ozgurgulsuna/ELE713-SwitchedPowerSupplies/[03] Simulation/Close-Loop-Forward-Converter-CONTROL.asc

B1: bv; V=V(Vi)
B3: bv; V= if(V(Vin) >50,0, 5)
C1: cap; {Cf}; Rser=28m
C2: cap; 100µ
C3: cap; 2.2n
C4: cap; 2.2n
C5: cap; 0.1µ
C6: cap; 22µ
C7: cap; 10n
C8: cap; 10n
D1: diode
D2: diode; RFUH25NS3S
D156: diode; D1
ind1: ind2; {L1}; Rser=20m
ind2: ind2; {L2}; Rser=20m
ind3: ind2; {L3}; Rser=20m
L4: ind2; {Lf}; Rser=15m
M1: nmos; IPB200N25N3
R1: res; 100
R2: res; {10*RL}
R4: res; 47
R5: res; 4.7k
R6: res; 100k
R7: res; 160k
R8: res; 178k
R9: res; 12k
R10: res; 18k
R11: res; 240k
R12: res; 10k
R13: res; 25k
R14: res; 10k
R15: res; 8.2k
R16: res; 4.7k
R17: res; 20k
R20: res; 39
R21: res; 1Meg
R22: res; 10k
R24: res; 0.6944
R26: res; 0
R30: res; 10k
Rs: res; 8m
S1: sw; NMOS
U1: LT1952-1
U3: tl431
U5: PC817C
V1: voltage; 11
V2: voltage; 12
Vi: voltage; PWL(0 0 0.499m 0 0.5m 36 1m 36 2m 36 2.01m 60)
Named nets: Vaux, 0, FB, Vref, SEC, Vi, Vin, VccBias, Sout, FWD
.model NMOS SW(Ron=25m Roff=1Meg Vt=.5 Vh=-.4)
.model D1 D(Ron=20m Roff=100G Vfwd=0.1)
.tran 0 0.1 0 1e-7 startup
K1 ind1 ind2 ind3 1
.param L1 190u
.param L2  30.4u
.param L3 190u
.param L4 94u
.param fs  200k
.param Cf 220u
.param RL 0.625
.param Lf 20u
.param Laux 20u
.param Caux 20u
.ic V(C10) = 8
.ic V(Vaux) = 8
.ic V(C2) = 8
.model HAT2266 VDMOS(Rg=0.5 Vto=2.3 Rd=4m Rs=1m Rb=5m Kp=70 lambda=.05 Cgdmax=0.65n Cgdmin=.08n Cgs=3.455n Cjo=1.2n Is=120p ksubthres=.1 mfg=Furkan Vds=60 Ron=12m Qg=25n)
*****************************************************************************
* TL431 MACROMODEL ***************3-26-92************************************
* REV N/A ****************************************************************DBB
*****************************************************************************
*               REFERENCE
*               |  ANODE
*               |  |  CATHODE
*               |  |  |
*.SUBCKT  TL431 1  2  3
* Reverse symbol
* Anode Cathode Ref   adjusted to LTSPICE symbol
.SUBCKT  TL431 2 3 1
V1  6  7  DC  1.4V
I1  2  4  1E-3
R1  1  2  1.2E6
R2  4  2  RMOD 2.495E3
R3  5  7  .2
D1  3  6  DMOD1
D2  2  3  DMOD1
D3  2  7  DMOD2
E1  5  2  POLY(2)  (4,2)  (1,2)  0  710  -710
.MODEL RMOD RES (TC1=1.4E-5 TC2=-1E-6)
.MODEL DMOD1 D (RS=.3)
.MODEL DMOD2 D (RS=1E-6)
.ENDS
