ozgurgulsuna/ELE713-SwitchedPowerSupplies/[03] Simulation/Close-Loop-Forward-Converter-REALISTIC.asc

B1: bv; V=V(Vi)
B2: bv; V=if(V(Vc,SEC)<12, V(Vc,SEC), 12)
B3: bv; V= if(V(Vin) >50,0, 5)
C1: cap; {Cf}; Rser=28m
C2: cap; 100µ
C3: cap; 2.2n
C4: cap; 2.2n
C5: cap; 0.1µ
C6: cap; 22µ
C7: cap; 5n
C8: cap; 1n
C9: cap; 22µ; Rser=2m
C10: cap; 1µ
C12: cap; 10µ
C13: cap; 220pF
C14: cap; 10µ
C15: cap; 100p
C16: cap; 1µ
Ctmr1: cap; 0.47n
D1: diode; 1N4148
D2: diode; RFUH25NS3S
D3: diode; 1N4148
D4: diode; D1
D5: zener; UDZV12B
D6: zener; PDZV16B
D7: diode; D1
D8: zener; TDZV9_1
D9: diode; D1
D11: diode; D1
ind1: ind2; {L1}; Rser=20m
ind2: ind2; {L2}; Rser=20m
ind3: ind2; {L3}; Rser=20m
ind4: ind2; {L4}; Rser=20m
ind5: ind2; {L4}; Rser=20m
L1: ind; 16µ
L2: ind; 16µ
L3: ind2; 300µ; Rser=13m
L4: ind2; {Lf}; Rser=15m
L5: ind2; 300µ; Rser=7m
L6: ind; 50n
M1: nmos; IPB200N25N3
M4: nmos; HAT2266
M5: nmos; HAT2266
Q1: pnp; BC856B
Q2: npn; 2SC5824
Q3: npn; 2SC5824
R1: res; 10k
R2: res; {10*RL}
R3: res; 220
R4: res; 47
R5: res; 1.2k
R6: res; 100k
R7: res; 160k
R8: res; 178k
R9: res; 12k
R10: res; 18k
R11: res; 240k
R12: res; 10k
R13: res; 100k
R14: res; 100k
R15: res; 22k
R16: res; 1k
R17: res; 4.7k
R18: res; 4.7k
R19: res; 4.7k
R20: res; 39
R21: res; 1
R22: res; 10k
R23: res; 1
R24: res; 0.6944
R25: res; 200
R26: res; 0
R27: res; 25
R28: res; 25
R29: res; 2.2k
R31: res; 10k
R32: res; 10k
R33: res; 1
R34: res; 10k
Rcs1: res; 365
Rcs2: res; 360
Rcs3: res; 182
Rs: res; 8m
Rtmr1: res; 100k
S1: sw; NMOS
TL1: tl431
TL431: tl431
U1: LT1952-1
U4: LTC3900
U5: PC817C
V1: voltage; 25
Vi: voltage; PWL(0 0 0.499m 0 0.5m 36 1m 36 2m 36 2.01m 60)
Named nets: Vaux, 0, FB, Vref, SEC, Vi, Vin, Vc, FWD, FG, CG, Sout, VccBias, 8v
.model NMOS SW(Ron=25m Roff=1Meg Vt=.5 Vh=-.4)
.model D1 D(Ron=20m Roff=100G Vfwd=0.1)
.tran 0 0.1 0  startup
K1 ind1 ind2 ind3 ind4 ind5 1
K2 L3 L5 1
.param L1 190u
.param L2  30.4u
.param L3 190u
.param L4 94u
.param fs  200k
.param Cf 220u
.param RL 0.625
.param Lf 20u
.param Laux 20u
.param Caux 20u
.ic V(C10) = 8
.ic V(Vaux) = 8
.ic V(C2) = 8
.model HAT2266 VDMOS(Rg=0.5 Vto=2.3 Rd=4m Rs=1m Rb=5m Kp=70 lambda=.05 Cgdmax=0.65n Cgdmin=.08n Cgs=3.455n Cjo=1.2n Is=120p ksubthres=.1 mfg=Furkan Vds=60 Ron=12m Qg=25n)
.lib tl431.lib
.include tl431.mod
