ozgurgulsuna/ELE713-SwitchedPowerSupplies/[03] Simulation/Close-Loop-Forward-Converter-2.asc

B1: bv; V=V(Vi)
C1: cap; {Cf}; Rser=50m
C2: cap; 2.2n
C3: cap; 2.2n
C4: cap; 220n
C5: cap; 0.1µ
C6: cap; 10p
C7: cap; 4.7n
C9: cap; {Caux}; Rser=2m
C11: cap; 10µ
C12: cap; 0.1µ
C13: cap; 4.7µ
D1: diode; D1
D2: diode; D1
D3: diode; D1
D4: diode; D1
D5: diode; D1
D6: diode; D1
D7: zener; EDZV18B
D8: schottky; MBR0540
D9: zener; BZX84B9V1LY
D12: zener; MMBZ16VALY
ind1: ind2; {L1}; Rser=20m
ind2: ind2; {L2}; Rser=20m
ind3: ind2; {L3}; Rser=20m
ind4: ind2; {L4}; Rser=20m
L1: ind; {Laux}; Rser=50m
L4: ind; {Lf}; Rser=50m
M1: nmos; IPB200N25N3
Q1: pnp; BC856B
Q2: npn; 2SCR513P
Q4: npn; 2SCR513P
R1: res; 33k
R2: res; {RL}
R3: res; 220
R4: res; 10
R5: res; 1k
R6: res; 100k
R7: res; 160k
R8: res; 180k
R9: res; 12k
R10: res; 18k
R11: res; 240k
R12: res; 10k
R13: res; 200K
R14: res; 27.2k
R15: res; 8.2k
R16: res; 470
R17: res; 22k
R18: res; 220
R19: res; 2.2
R20: res; 1k
R21: res; 1Meg
R22: res; 10k
R23: res; 1k
R27: res; 82k
Raux: res; 36
Rs: res; 10m
U1: LT1952-1
U2: LT4430
U3: 4N25
U4: LT1086-12
V1: voltage; PULSE(8 8 0 1n 1n 1)
V3: voltage; PULSE(0 12 1m 1n 1n 1)
Vi: voltage; PWL(0 0 1m 0 1.01m 48 3m 48 3m 48 3.01m 60)
Named nets: Vaux, 0, Sout, FB, Vref, SEC, Vbias, Vi, Vout
.model NMOS SW(Ron=25m Roff=1Meg Vt=.5 Vh=-.4)
.model D1 D(Ron=20m Roff=100G Vfwd=0.1)
.tran 0 0.05 0 1e-7
K1 ind1 ind2 ind3  ind4 1
.param L1 190u
.param L2  30.4u
.param L3 190u
.param L4 121.6u
.param fs  200k
.param Cf 100u
.param RL 0.625
.param Lf 16u
.param Laux 20u
.param Caux 47u
.ic V(Vaux) = 0
.ic V(C11) = 0
