ozgurgulsuna/ELE713-SwitchedPowerSupplies/[03] Simulation/Close-Loop-Forward-Converter.asc

B1: bv; V={Vi}
C1: cap; {Cf}; Rser=2m
C2: cap; {Caux}; Rser=2m
C3: cap; 2.2n
C4: cap; 0.22µ
C5: cap; 0.1µ
C6: cap; 10p
C7: cap; 4.7n
C8: cap; 10n
D1: diode; D1
D2: diode; D1
D3: diode; D1
D4: diode; D1
D5: diode; D1
D6: zener; MMBZ16VALY
ind1: ind2; {L1}; Rser=20m
ind2: ind2; {L2}; Rser=20m
ind3: ind2; {L3}; Rser=20m
ind4: ind2; {L4}; Rser=20m
L1: ind; {Laux}; Rser=50m
L4: ind; {Lf}; Rser=50m
M1: nmos; BSC900N20NS3
Q1: npn; 2N2222
Q2: pnp; BC856B
R1: res; 36
R2: res; {RL}
R3: res; 1.5k
R4: res; 10
R5: res; 33k
R6: res; 200K
R7: res; 100K
R8: res; 200k
R9: res; 11K
R10: res; 12.4K
R11: res; 240K
R12: res; {240K/24}
R13: res; 200K
R14: res; 27.2K
R15: res; 8.2K
R16: res; 470
R17: res; 220
R18: res; 1.2k
R19: res; 22K
R20: res; 1Meg
R21: res; 1Meg
R22: res; 10k
Rs: res; 10m
U1: LT1952-1
U2: LT4430
U3: 4N25
V1: voltage; 12
V2: voltage; 5
Named nets: 0, Vaux, COM, Sout, FB, Vref, SEC, Vbias
.model NMOS SW(Ron=25m Roff=1Meg Vt=.5 Vh=-.4)
.model D1 D(Ron=20m Roff=100G Vfwd=0.1)
.tran 0 0.011 0
K1 ind1 ind2 ind3 ind4 1
.param L1 185.6u
.param L2  26.1u 
.param L3 185.6u
.param L4 104.4u
.param fs  200k
.param Cf 15u
.param RL 0.625
.param Lf 16u
.param Laux 20u
.param Caux 20u
.param Vi 60
.param D 0.22
