ozgurgulsuna/ELE713-SwitchedPowerSupplies/[03] Simulation/Forward-Converter.asc

B1: bv; V={Vi}
C1: cap; {Cf}; Rser=2m
C2: cap; {Caux}; Rser=2m
D1: diode; D1
D2: diode; D1
D3: diode; D1
D4: diode; D1
D5: diode; D1
D6: zener; MMBZ16VALY
ind1: ind2; {L1}; Rser=20m
ind2: ind2; {L2}; Rser=20m
ind3: ind2; {L3}; Rser=20m
ind4: ind2; {L4}; Rser=20m
L1: ind; {Laux}; Rser=50m
L4: ind; {Lf}; Rser=50m
Q1: npn; 2N2222
R1: res; 36
R2: res; {RL}
R3: res; 1.5k
R4: res; 1Meg
R5: res; 1Meg
sw: sw; NMOS
V2: voltage; PULSE(0 1 0 1n 1n {D*1/fs} {1/fs})
Named nets: 0
.model NMOS SW(Ron=25m Roff=1Meg Vt=.5 Vh=-.4)
.model D1 D(Ron=20m Roff=100G Vfwd=0.1)
.tran 0 0.011 0.01 0.01u
K1 ind1 ind2 ind3 ind4 1
.param L1 185.6u
.param L2  26.1u 
.param L3 185.6u
.param L4 104.4u
.param fs  200k
.param Cf 15u
.param RL 0.625
.param Lf 16u
.param Laux 20u
.param Caux 20u
.param Vi 60
.param D 0.22
