ozgurgulsuna/ELE713-SwitchedPowerSupplies/[03] Simulation/Forward.asc

C1: cap; 10p
C2: cap; 660µ; Rser=17.67m
C3: cap; 0.1µ
C4: cap; 0.22µ
C5: cap; 220pF
C6: cap; 0.1µ
C7: cap; 4.7µ
C8: cap; 33µ
C9: cap; 100µF; IC={-12.3}
C10: cap; 4.7n
C11: cap; 1µ
C12: cap; 33n
C13: cap; 2.2nF
C14: cap; 4700p
C15: cap; 10µ
C16: cap; 1µ
C17: cap; 100p
Ctmr: cap; 0.47n
D1: schottky; MBR0540
D2: zener; KDZ7_5B
D3: diode
D4: diode; BAS16HM
D5: zener; UMZ13K
D6: zener; EDZV18B
L1: ind2; 290µ; Rser=13m
L2: ind2; 46.4µ; Rser=7m
L3: ind2; 290µ; Rser=16m
L4: ind2; 72.5µ; Rser=10m
L5: ind; 10µ; Rser=6.33m
L6: ind2; 300µ; Rser=13m
L7: ind2; 300µ; Rser=7m
L9: ind; 50n
M1: nmos; HAT2266
M2: nmos; HAT2266
M3: nmos
Q1: npn; 2SCR513P
Q2: npn; 2SCR513P
Q3: pnp; BC856B
R1: res; 240k
R2: res; {240K/24}
R3: res; 200
R4: res; 8.2k
R5: res; 0.5
R6: res; 464
R7: res; 200k
R8: res; 27.2k
R9: res; 22k
R10: res; 33k
R11: res; 99Meg
R12: res; 1k
R13: res; 200k
R14: res; 2.2
R15: res; 47k
R16: res; 82k
R17: res; 1.2k
R18: res; 220
R19: res; 0.1µ
R20: res; 40
R21: res; 47
R22: res; 4.7k
Rb: res; 12.4k
Rcs1: res; 365
Rcs2: res; 360
Rcs3: res; 182
Rdelay: res; 100k
Rload: res; R={5/8}
Rosc: res; 301k
Rs: res; 10m; tol=1 pwr=1
Rt: res; 11k
Rtmr: res; 90.9k
U1: LT1952-1
U2: LTC3900
U3: PS2801
U4: LT4430
U5: LT1086-12
V1: voltage; 36; AC 0
V2: voltage; PULSE(8 0.8 6m 1u 1u 6m 12m)
V3: voltage; PULSE(36 60 6m 1u 1u 6m 12m)
Named nets: 0, COM, IN, OUT, FWD, FG, CG, Sout, VccBias, FB, SEC, Vu1, Vref, Current, Vreg
.tran 0 1500m 0 1e-7 startup
K1 L1 L2 1
K2 L1 L3 1
K3 L1 L4 1
K4 L2 L3 1
K5 L2 L4 1
K6 L3 L4 1
K7 L6 L7 1
L1 - Primer
L2 - Seconder
L3 - Aux
L4 - Reset
.model HAT2266 VDMOS(Rg=0.5 Vto=2.3 Rd=4m Rs=1m Rb=5m Kp=70 lambda=.05 Cgdmax=0.65n Cgdmin=.08n Cgs=3.455n Cjo=1.2n Is=120p ksubthres=.1 mfg=Furkan Vds=60 Ron=12m Qg=25n)
.model NMOS VDMOS(Rg=3 Rd=1.2m Rs=.9m Vto=1.2 Kp=50 Cgdmax=2n Cgdmin=.25n Cgs=3.3n Cjo=1n Is=100p Rb=1.5m ksubthres=.1 mfg=Siliconix Vds=20 Ron=3m Qg=50n)
